CasualCodersProjects/Keyboard/Hardware/100p-keebored.kicad_sch

## KiCad design Hardware/100p-keebored.kicad_sch (2023-06-21)

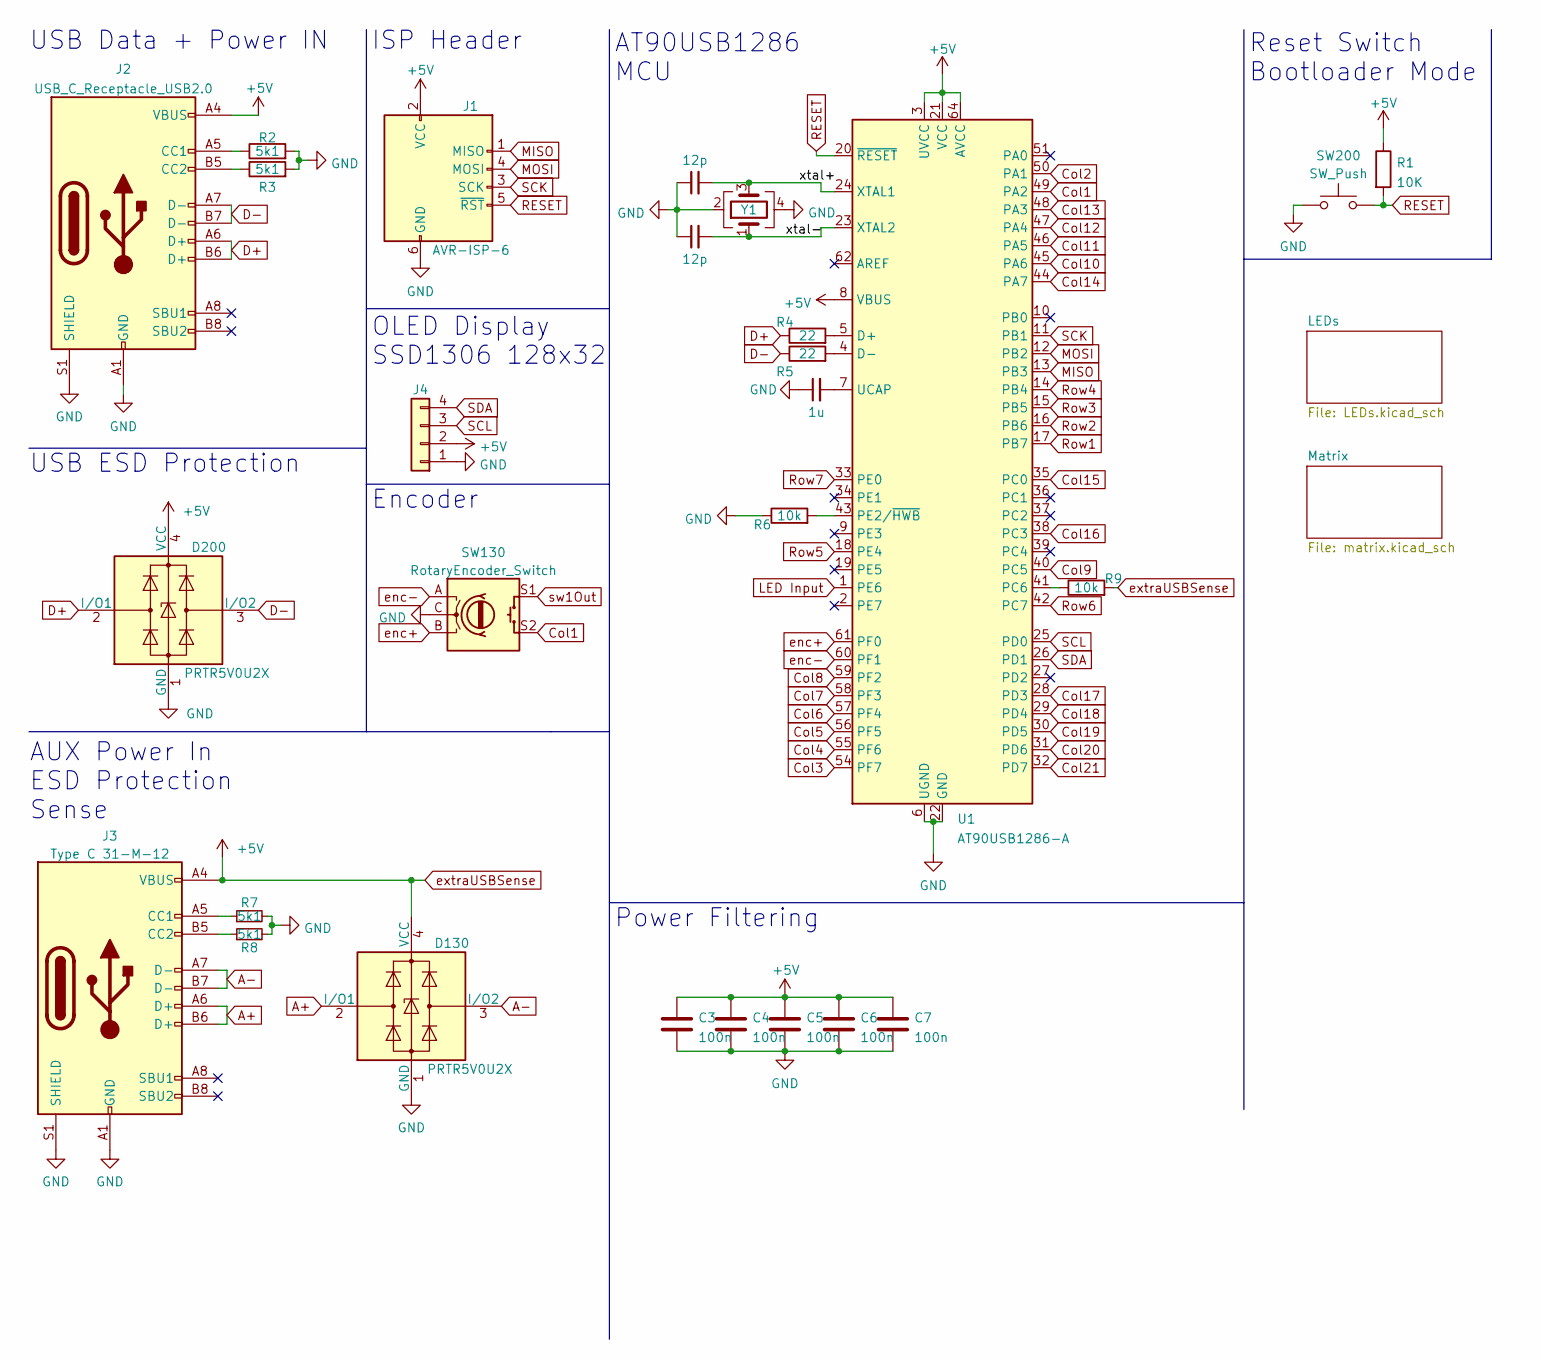
[picture p3: schematic 100p-keebored.kicad_sch]

Parts:
C1, C2: 12p; C_0402_1005Metric
C3, C4, C5, C6, C7: 100n; C_0402_1005Metric
C8: 1u; C_0402_1005Metric
D130, D200: PRTR5V0U2X; SOT-143
J1: AVR-ISP-6; Tag-Connect_TC2030-IDC-NL_2x03_P1.27mm_Vertical
J2: USB_C_Receptacle_USB2.0; USB_C_Receptacle_HRO_TYPE-C-31-M-12
J3: Type C 31-M-12; USB_C_Receptacle_HRO_TYPE-C-31-M-12
J4: Conn_01x04; SSD1306_128_32
R1: 10K; R_0402_1005Metric
R2, R3, R7, R8: 5k1; R_0402_1005Metric
R4, R5: 22; R_0402_1005Metric
R6, R9: 10k; R_0402_1005Metric
SW130: RotaryEncoder_Switch; RotaryEncoder_Alps_EC11E-Switch_Vertical_H20mm
SW200: SW_Push; SW_SPST_SKQG_WithStem
U1: AT90USB1286-A; TQFP-64_14x14mm_P0.8mm
Y1: JYJE 3TJ480000JYLBC; Crystal_SMD_3225-4Pin_3.2x2.5mm

Connections:
+5V: C3.1, C4.1, C5.1, C6.1, C7.1, D130.4 (VCC), D200.4 (VCC), J1.2 (VCC), J2.A4 (VBUS), J2.A9 (VBUS), J2.B4 (VBUS), J2.B9 (VBUS), J3.A4 (VBUS), J3.A9 (VBUS), J3.B4 (VBUS), J3.B9 (VBUS), J4.2, R1.1, R9.2, U1.3 (UVCC), U1.8 (VBUS), U1.21 (VCC), U1.52 (VCC), U1.64 (AVCC)
A+: D130.2 (I/O1), J3.A6 (D+), J3.B6 (D+)
A-: D130.3 (I/O2), J3.A7 (D-), J3.B7 (D-)
Col1: SW130.S2, U1.49 (PA2)
Col2: U1.50 (PA1)
Col3: U1.54 (PF7)
Col4: U1.55 (PF6)
Col5: U1.56 (PF5)
Col6: U1.57 (PF4)
Col7: U1.58 (PF3)
Col8: U1.59 (PF2)
Col9: U1.40 (PC5)
Col10: U1.45 (PA6)
Col11: U1.46 (PA5)
Col12: U1.47 (PA4)
Col13: U1.48 (PA3)
Col14: U1.44 (PA7)
Col15: U1.35 (PC0)
Col16: U1.38 (PC3)
Col17: U1.28 (PD3)
Col18: U1.29 (PD4)
Col19: U1.30 (PD5)
Col20: U1.31 (PD6)
Col21: U1.32 (PD7)
D+: D200.2 (I/O1), J2.A6 (D+), J2.B6 (D+), R4.1
D-: D200.3 (I/O2), J2.A7 (D-), J2.B7 (D-), R5.1
GND: C1.1, C2.1, C3.2, C4.2, C5.2, C6.2, C7.2, C8.1, D130.1 (GND), D200.1 (GND), J1.6 (GND), J2.A1 (GND), J2.A12 (GND), J2.B1 (GND), J2.B12 (GND), J2.S1 (SHIELD), J3.A1 (GND), J3.A12 (GND), J3.B1 (GND), J3.B12 (GND), J3.S1 (SHIELD), J4.1, R2.2, R3.2, R6.1, R7.2, R8.2, SW130.C, SW200.1, U1.6 (UGND), U1.22 (GND), U1.53 (GND), U1.63 (GND), Y1.2, Y1.4
LED Input: U1.1 (PE6)
MISO: J1.1 (MISO), U1.13 (PB3)
MOSI: J1.4 (MOSI), U1.12 (PB2)
unnamed: C8.2, U1.7 (UCAP)
unnamed: J2.A5 (CC1), R2.1
unnamed: J2.B5 (CC2), R3.1
unnamed: J3.A5 (CC1), R7.1
unnamed: J3.B5 (CC2), R8.1
unnamed: R4.2, U1.5 (D+)
unnamed: R5.2, U1.4 (D-)
unnamed: R6.2, U1.43 (PE2/~HWB)
unnamed: R9.1, U1.41 (PC6)
RESET: J1.5 (~RST), R1.2, SW200.2, U1.20 (~RESET)
Row1: U1.17 (PB7)
Row2: U1.16 (PB6)
Row3: U1.15 (PB5)
Row4: U1.14 (PB4)
Row5: U1.18 (PE4)
Row6: U1.42 (PC7)
Row7: U1.33 (PE0)
SCK: J1.3 (SCK), U1.11 (PB1)
SCL: J4.3, U1.25 (PD0)
SDA: J4.4, U1.26 (PD1)
enc+: SW130.B, U1.61 (PF0)
enc-: SW130.A, U1.60 (PF1)
sw1Out: SW130.S1
xtal+: C2.2, U1.24 (XTAL1), Y1.3
xtal-: C1.2, U1.23 (XTAL2), Y1.1

Notes on the sheet:
USB Data + Power IN
Encoder
OLED Display SSD1306 128x32
Power Filtering
AT90USB1286 MCU
AUX Power In ESD Protection Sense
ISP Header
USB ESD Protection
Reset Switch Bootloader Mode
