CasualCodersProjects/Keyboard/Hardware/LEDs.kicad_sch

## KiCad design Hardware/LEDs.kicad_sch (2023-06-21)

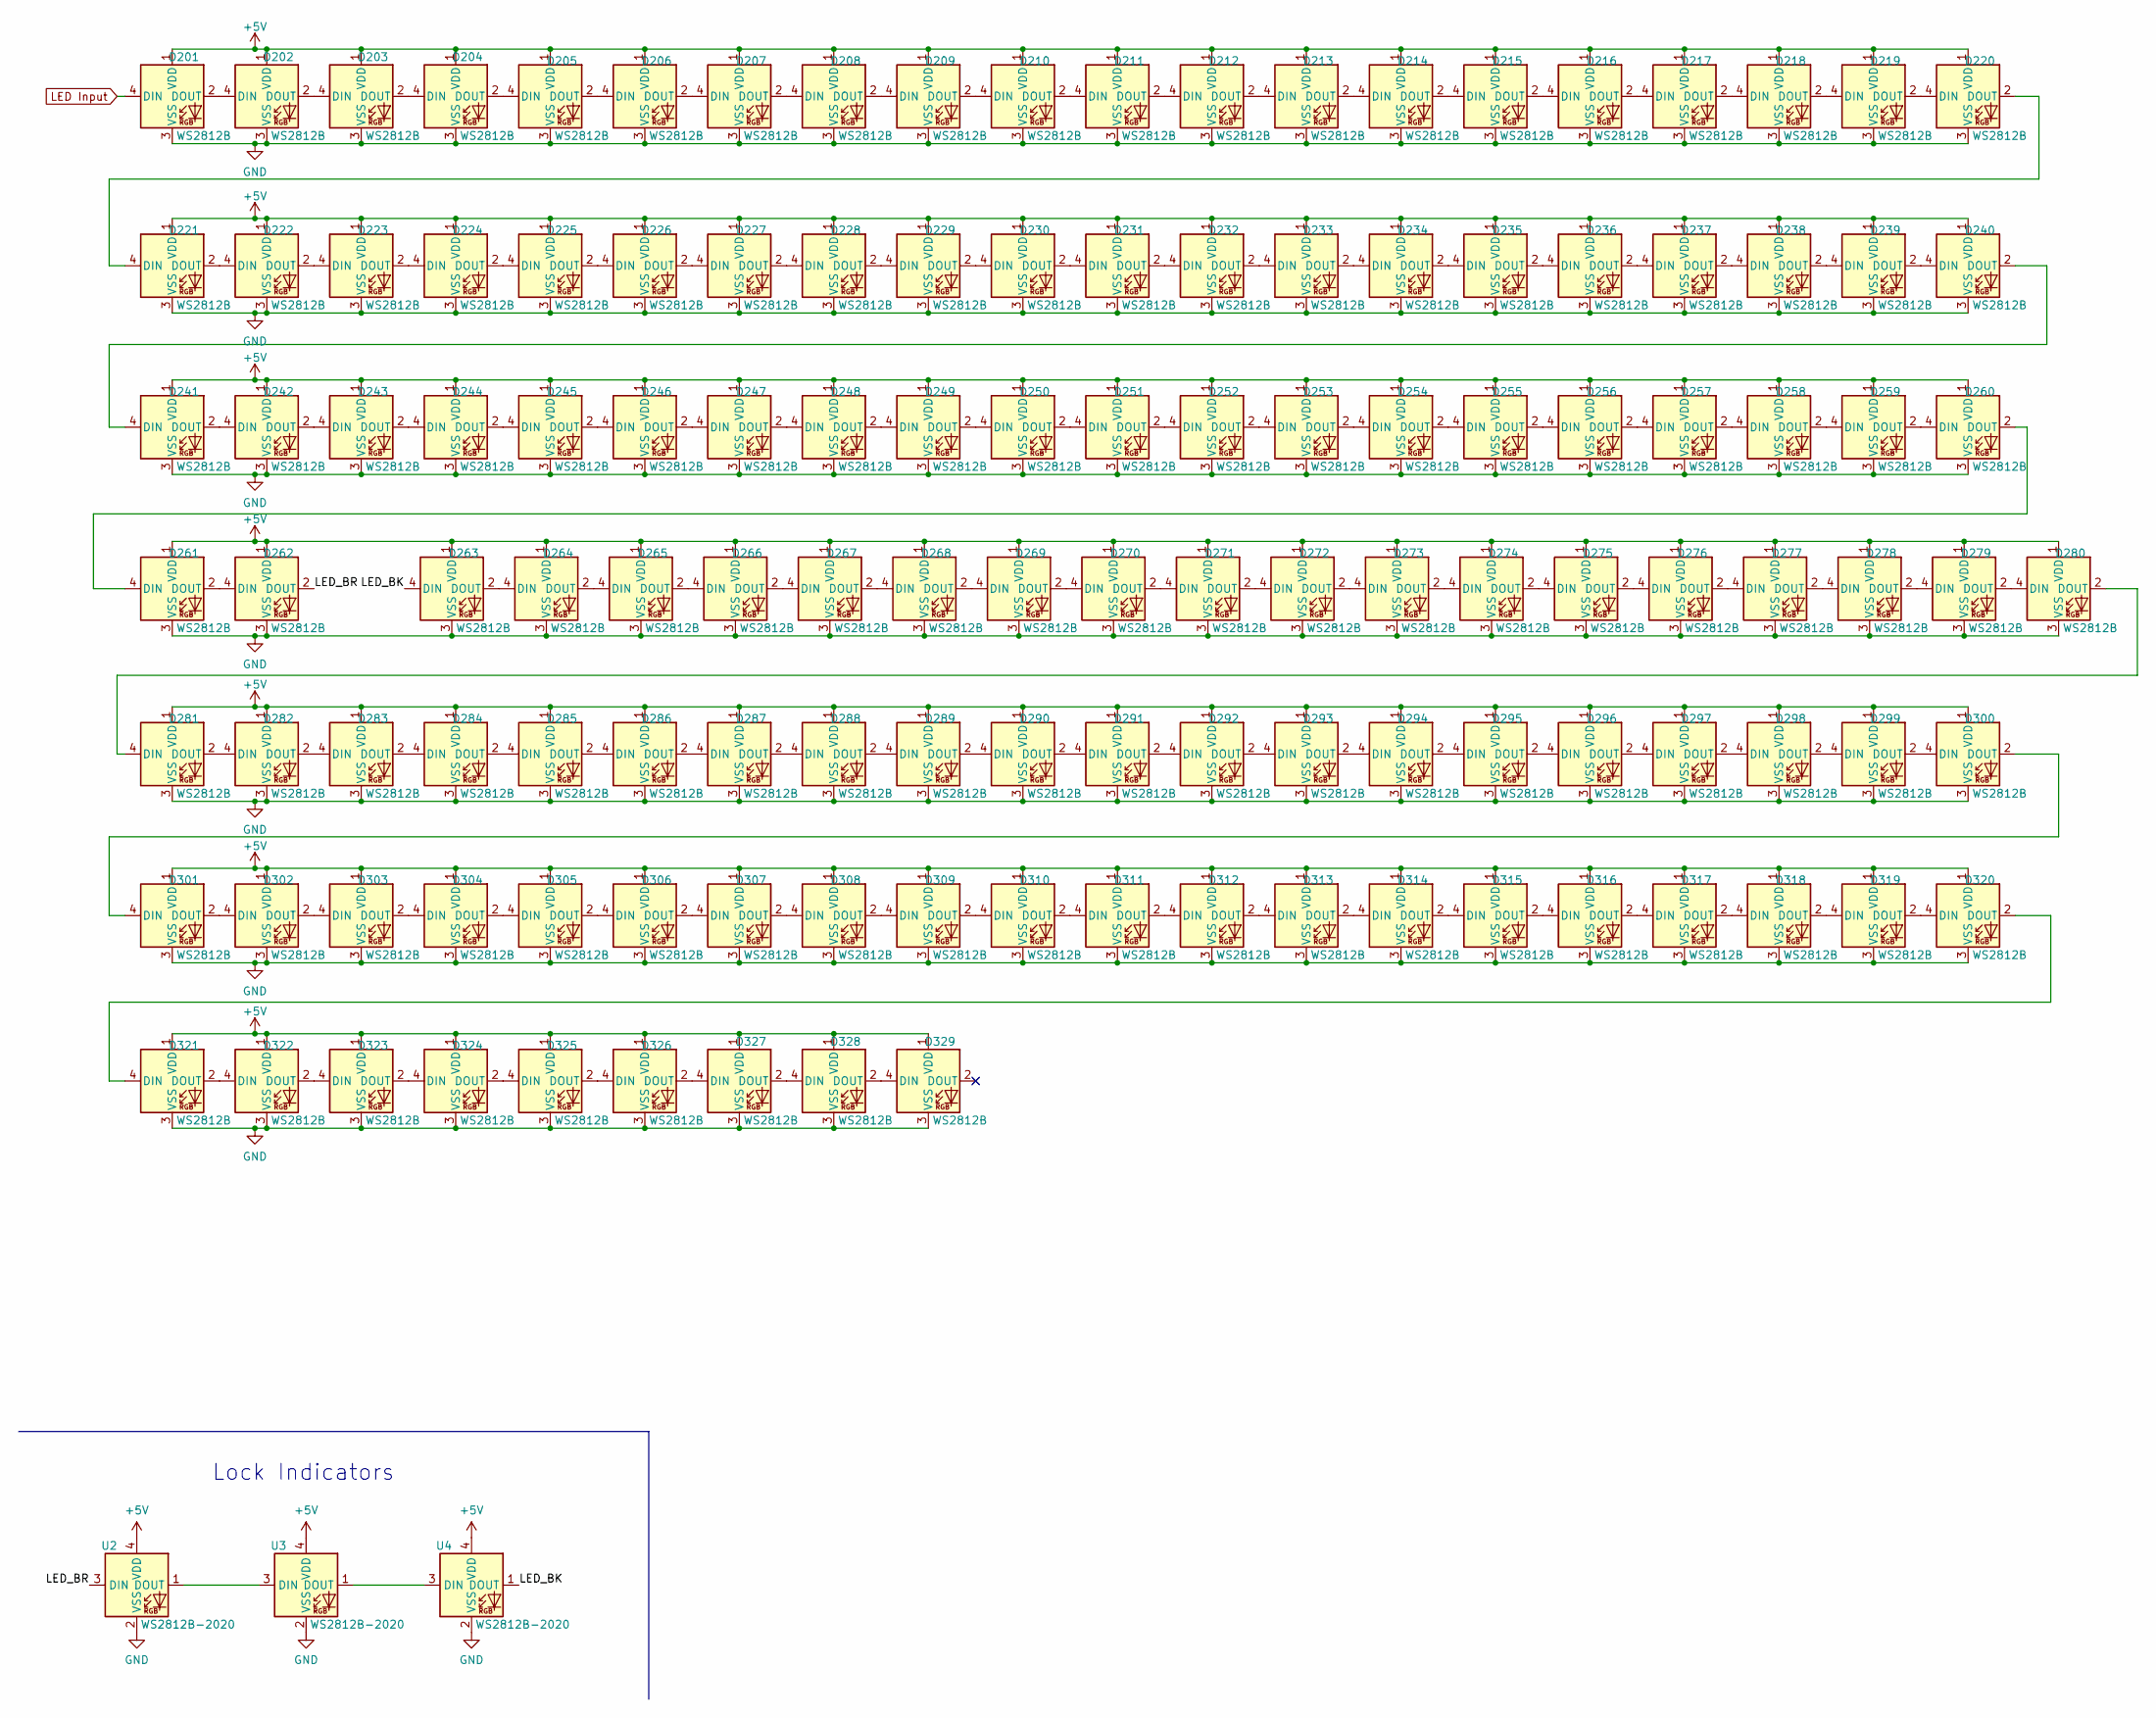
[picture p4: schematic LEDs.kicad_sch]

Parts:
D201, D202, D203, D204, D205, D206, D207, D208, D209, D210, D211, D212, D213, D214, D215, D216, D217, D218, D219, D220, D221, D222, D223, D224, D225, D226, D227, D228, D229, D230, D231, D232, D233, D234, D235, D236, D237, D238, D239, D240, D241, D242, D243, D244, D245, D246, D247, D248, D249, D250, D251, D252, D253, D254, D255, D256, D257, D258, D259, D260, D261, D262, D263, D264, D265, D266, D267, D268, D269, D270, D271, D272, D273, D274, D275, D276, D277, D278, D279, D280, D281, D282, D283, D284, D285, D286, D287, D288, D289, D290, D291, D292, D293, D294, D295, D296, D297, D298, D299, D300, D301, D302, D303, D304, D305, D306, D307, D308, D309, D310, D311, D312, D313, D314, D315, D316, D317, D318, D319, D320, D321, D322, D323, D324, D325, D326, D327, D328, D329: WS2812B; WS2812B-2020 ShineThrough
U2, U3, U4: WS2812B-2020; LED_WS2812B-2020_PLCC4_2.0x2.0mm

Connections:
+5V: D201.1 (VDD), D202.1 (VDD), D203.1 (VDD), D204.1 (VDD), D205.1 (VDD), D206.1 (VDD), D207.1 (VDD), D208.1 (VDD), D209.1 (VDD), D210.1 (VDD), D211.1 (VDD), D212.1 (VDD), D213.1 (VDD), D214.1 (VDD), D215.1 (VDD), D216.1 (VDD), D217.1 (VDD), D218.1 (VDD), D219.1 (VDD), D220.1 (VDD), D221.1 (VDD), D222.1 (VDD), D223.1 (VDD), D224.1 (VDD), D225.1 (VDD), D226.1 (VDD), D227.1 (VDD), D228.1 (VDD), D229.1 (VDD), D230.1 (VDD), D231.1 (VDD), D232.1 (VDD), D233.1 (VDD), D234.1 (VDD), D235.1 (VDD), D236.1 (VDD), D237.1 (VDD), D238.1 (VDD), D239.1 (VDD), D240.1 (VDD), D241.1 (VDD), D242.1 (VDD), D243.1 (VDD), D244.1 (VDD), D245.1 (VDD), D246.1 (VDD), D247.1 (VDD), D248.1 (VDD), D249.1 (VDD), D250.1 (VDD), D251.1 (VDD), D252.1 (VDD), D253.1 (VDD), D254.1 (VDD), D255.1 (VDD), D256.1 (VDD), D257.1 (VDD), D258.1 (VDD), D259.1 (VDD), D260.1 (VDD), D261.1 (VDD), D262.1 (VDD), D263.1 (VDD), D264.1 (VDD), D265.1 (VDD), D266.1 (VDD), D267.1 (VDD), D268.1 (VDD), D269.1 (VDD), D270.1 (VDD), D271.1 (VDD), D272.1 (VDD), D273.1 (VDD), D274.1 (VDD), D275.1 (VDD), D276.1 (VDD), D277.1 (VDD), D278.1 (VDD), D279.1 (VDD), D280.1 (VDD), D281.1 (VDD), D282.1 (VDD), D283.1 (VDD), D284.1 (VDD), D285.1 (VDD), D286.1 (VDD), D287.1 (VDD), D288.1 (VDD), D289.1 (VDD), D290.1 (VDD), D291.1 (VDD), D292.1 (VDD), D293.1 (VDD), D294.1 (VDD), D295.1 (VDD), D296.1 (VDD), D297.1 (VDD), D298.1 (VDD), D299.1 (VDD), D300.1 (VDD), D301.1 (VDD), D302.1 (VDD), D303.1 (VDD), D304.1 (VDD), D305.1 (VDD), D306.1 (VDD), D307.1 (VDD), D308.1 (VDD), D309.1 (VDD), D310.1 (VDD), D311.1 (VDD), D312.1 (VDD), D313.1 (VDD), D314.1 (VDD), D315.1 (VDD), D316.1 (VDD), D317.1 (VDD), D318.1 (VDD), D319.1 (VDD), D320.1 (VDD), D321.1 (VDD), D322.1 (VDD), D323.1 (VDD), D324.1 (VDD), D325.1 (VDD), D326.1 (VDD), D327.1 (VDD), D328.1 (VDD), D329.1 (VDD), U2.4 (VDD), U3.4 (VDD), U4.4 (VDD)
GND: D201.3 (VSS), D202.3 (VSS), D203.3 (VSS), D204.3 (VSS), D205.3 (VSS), D206.3 (VSS), D207.3 (VSS), D208.3 (VSS), D209.3 (VSS), D210.3 (VSS), D211.3 (VSS), D212.3 (VSS), D213.3 (VSS), D214.3 (VSS), D215.3 (VSS), D216.3 (VSS), D217.3 (VSS), D218.3 (VSS), D219.3 (VSS), D220.3 (VSS), D221.3 (VSS), D222.3 (VSS), D223.3 (VSS), D224.3 (VSS), D225.3 (VSS), D226.3 (VSS), D227.3 (VSS), D228.3 (VSS), D229.3 (VSS), D230.3 (VSS), D231.3 (VSS), D232.3 (VSS), D233.3 (VSS), D234.3 (VSS), D235.3 (VSS), D236.3 (VSS), D237.3 (VSS), D238.3 (VSS), D239.3 (VSS), D240.3 (VSS), D241.3 (VSS), D242.3 (VSS), D243.3 (VSS), D244.3 (VSS), D245.3 (VSS), D246.3 (VSS), D247.3 (VSS), D248.3 (VSS), D249.3 (VSS), D250.3 (VSS), D251.3 (VSS), D252.3 (VSS), D253.3 (VSS), D254.3 (VSS), D255.3 (VSS), D256.3 (VSS), D257.3 (VSS), D258.3 (VSS), D259.3 (VSS), D260.3 (VSS), D261.3 (VSS), D262.3 (VSS), D263.3 (VSS), D264.3 (VSS), D265.3 (VSS), D266.3 (VSS), D267.3 (VSS), D268.3 (VSS), D269.3 (VSS), D270.3 (VSS), D271.3 (VSS), D272.3 (VSS), D273.3 (VSS), D274.3 (VSS), D275.3 (VSS), D276.3 (VSS), D277.3 (VSS), D278.3 (VSS), D279.3 (VSS), D280.3 (VSS), D281.3 (VSS), D282.3 (VSS), D283.3 (VSS), D284.3 (VSS), D285.3 (VSS), D286.3 (VSS), D287.3 (VSS), D288.3 (VSS), D289.3 (VSS), D290.3 (VSS), D291.3 (VSS), D292.3 (VSS), D293.3 (VSS), D294.3 (VSS), D295.3 (VSS), D296.3 (VSS), D297.3 (VSS), D298.3 (VSS), D299.3 (VSS), D300.3 (VSS), D301.3 (VSS), D302.3 (VSS), D303.3 (VSS), D304.3 (VSS), D305.3 (VSS), D306.3 (VSS), D307.3 (VSS), D308.3 (VSS), D309.3 (VSS), D310.3 (VSS), D311.3 (VSS), D312.3 (VSS), D313.3 (VSS), D314.3 (VSS), D315.3 (VSS), D316.3 (VSS), D317.3 (VSS), D318.3 (VSS), D319.3 (VSS), D320.3 (VSS), D321.3 (VSS), D322.3 (VSS), D323.3 (VSS), D324.3 (VSS), D325.3 (VSS), D326.3 (VSS), D327.3 (VSS), D328.3 (VSS), D329.3 (VSS), U2.2 (VSS), U3.2 (VSS), U4.2 (VSS)
LED Input: D201.4 (DIN)
LED_BK: D263.4 (DIN), U4.1 (DOUT)
LED_BR: D262.2 (DOUT), U2.3 (DIN)
unnamed: D201.2 (DOUT), D202.4 (DIN)
unnamed: D202.2 (DOUT), D203.4 (DIN)
unnamed: D203.2 (DOUT), D204.4 (DIN)
unnamed: D204.2 (DOUT), D205.4 (DIN)
unnamed: D205.2 (DOUT), D206.4 (DIN)
unnamed: D206.2 (DOUT), D207.4 (DIN)
unnamed: D207.2 (DOUT), D208.4 (DIN)
unnamed: D208.2 (DOUT), D209.4 (DIN)
unnamed: D209.2 (DOUT), D210.4 (DIN)
unnamed: D210.2 (DOUT), D211.4 (DIN)
unnamed: D211.2 (DOUT), D212.4 (DIN)
unnamed: D212.2 (DOUT), D213.4 (DIN)
unnamed: D213.2 (DOUT), D214.4 (DIN)
unnamed: D214.2 (DOUT), D215.4 (DIN)
unnamed: D215.2 (DOUT), D216.4 (DIN)
unnamed: D216.2 (DOUT), D217.4 (DIN)
unnamed: D217.2 (DOUT), D218.4 (DIN)
unnamed: D218.2 (DOUT), D219.4 (DIN)
unnamed: D219.2 (DOUT), D220.4 (DIN)
unnamed: D220.2 (DOUT), D221.4 (DIN)
unnamed: D221.2 (DOUT), D222.4 (DIN)
unnamed: D222.2 (DOUT), D223.4 (DIN)
unnamed: D223.2 (DOUT), D224.4 (DIN)
unnamed: D224.2 (DOUT), D225.4 (DIN)
unnamed: D225.2 (DOUT), D226.4 (DIN)
unnamed: D226.2 (DOUT), D227.4 (DIN)
unnamed: D227.2 (DOUT), D228.4 (DIN)
unnamed: D228.2 (DOUT), D229.4 (DIN)
unnamed: D229.2 (DOUT), D230.4 (DIN)
unnamed: D230.2 (DOUT), D231.4 (DIN)
unnamed: D231.2 (DOUT), D232.4 (DIN)
unnamed: D232.2 (DOUT), D233.4 (DIN)
unnamed: D233.2 (DOUT), D234.4 (DIN)
unnamed: D234.2 (DOUT), D235.4 (DIN)
unnamed: D235.2 (DOUT), D236.4 (DIN)
unnamed: D236.2 (DOUT), D237.4 (DIN)
unnamed: D237.2 (DOUT), D238.4 (DIN)
unnamed: D238.2 (DOUT), D239.4 (DIN)
unnamed: D239.2 (DOUT), D240.4 (DIN)
unnamed: D240.2 (DOUT), D241.4 (DIN)
unnamed: D241.2 (DOUT), D242.4 (DIN)
unnamed: D242.2 (DOUT), D243.4 (DIN)
unnamed: D243.2 (DOUT), D244.4 (DIN)
unnamed: D244.2 (DOUT), D245.4 (DIN)
unnamed: D245.2 (DOUT), D246.4 (DIN)
unnamed: D246.2 (DOUT), D247.4 (DIN)
unnamed: D247.2 (DOUT), D248.4 (DIN)
unnamed: D248.2 (DOUT), D249.4 (DIN)
unnamed: D249.2 (DOUT), D250.4 (DIN)
unnamed: D250.2 (DOUT), D251.4 (DIN)
unnamed: D251.2 (DOUT), D252.4 (DIN)
unnamed: D252.2 (DOUT), D253.4 (DIN)
unnamed: D253.2 (DOUT), D254.4 (DIN)
unnamed: D254.2 (DOUT), D255.4 (DIN)
unnamed: D255.2 (DOUT), D256.4 (DIN)
unnamed: D256.2 (DOUT), D257.4 (DIN)
unnamed: D257.2 (DOUT), D258.4 (DIN)
unnamed: D258.2 (DOUT), D259.4 (DIN)
unnamed: D259.2 (DOUT), D260.4 (DIN)
unnamed: D260.2 (DOUT), D261.4 (DIN)
unnamed: D261.2 (DOUT), D262.4 (DIN)
unnamed: D263.2 (DOUT), D264.4 (DIN)
unnamed: D264.2 (DOUT), D265.4 (DIN)
unnamed: D265.2 (DOUT), D266.4 (DIN)
unnamed: D266.2 (DOUT), D267.4 (DIN)
unnamed: D267.2 (DOUT), D268.4 (DIN)
unnamed: D268.2 (DOUT), D269.4 (DIN)
unnamed: D269.2 (DOUT), D270.4 (DIN)
unnamed: D270.2 (DOUT), D271.4 (DIN)
unnamed: D271.2 (DOUT), D272.4 (DIN)
unnamed: D272.2 (DOUT), D273.4 (DIN)
unnamed: D273.2 (DOUT), D274.4 (DIN)
unnamed: D274.2 (DOUT), D275.4 (DIN)
unnamed: D275.2 (DOUT), D276.4 (DIN)
unnamed: D276.2 (DOUT), D277.4 (DIN)
unnamed: D277.2 (DOUT), D278.4 (DIN)
unnamed: D278.2 (DOUT), D279.4 (DIN)
unnamed: D279.2 (DOUT), D280.4 (DIN)
unnamed: D280.2 (DOUT), D281.4 (DIN)
unnamed: D281.2 (DOUT), D282.4 (DIN)
unnamed: D282.2 (DOUT), D283.4 (DIN)
unnamed: D283.2 (DOUT), D284.4 (DIN)
unnamed: D284.2 (DOUT), D285.4 (DIN)
unnamed: D285.2 (DOUT), D286.4 (DIN)
unnamed: D286.2 (DOUT), D287.4 (DIN)
unnamed: D287.2 (DOUT), D288.4 (DIN)
unnamed: D288.2 (DOUT), D289.4 (DIN)
unnamed: D289.2 (DOUT), D290.4 (DIN)
unnamed: D290.2 (DOUT), D291.4 (DIN)
unnamed: D291.2 (DOUT), D292.4 (DIN)
unnamed: D292.2 (DOUT), D293.4 (DIN)
unnamed: D293.2 (DOUT), D294.4 (DIN)
unnamed: D294.2 (DOUT), D295.4 (DIN)
unnamed: D295.2 (DOUT), D296.4 (DIN)
unnamed: D296.2 (DOUT), D297.4 (DIN)
unnamed: D297.2 (DOUT), D298.4 (DIN)
unnamed: D298.2 (DOUT), D299.4 (DIN)
unnamed: D299.2 (DOUT), D300.4 (DIN)
unnamed: D300.2 (DOUT), D301.4 (DIN)
unnamed: D301.2 (DOUT), D302.4 (DIN)
unnamed: D302.2 (DOUT), D303.4 (DIN)
unnamed: D303.2 (DOUT), D304.4 (DIN)
unnamed: D304.2 (DOUT), D305.4 (DIN)
unnamed: D305.2 (DOUT), D306.4 (DIN)
unnamed: D306.2 (DOUT), D307.4 (DIN)
unnamed: D307.2 (DOUT), D308.4 (DIN)
unnamed: D308.2 (DOUT), D309.4 (DIN)
unnamed: D309.2 (DOUT), D310.4 (DIN)
unnamed: D310.2 (DOUT), D311.4 (DIN)
unnamed: D311.2 (DOUT), D312.4 (DIN)
unnamed: D312.2 (DOUT), D313.4 (DIN)
unnamed: D313.2 (DOUT), D314.4 (DIN)
unnamed: D314.2 (DOUT), D315.4 (DIN)
unnamed: D315.2 (DOUT), D316.4 (DIN)
unnamed: D316.2 (DOUT), D317.4 (DIN)
unnamed: D317.2 (DOUT), D318.4 (DIN)
unnamed: D318.2 (DOUT), D319.4 (DIN)
unnamed: D319.2 (DOUT), D320.4 (DIN)
unnamed: D320.2 (DOUT), D321.4 (DIN)
unnamed: D321.2 (DOUT), D322.4 (DIN)
unnamed: D322.2 (DOUT), D323.4 (DIN)
unnamed: D323.2 (DOUT), D324.4 (DIN)
unnamed: D324.2 (DOUT), D325.4 (DIN)
unnamed: D325.2 (DOUT), D326.4 (DIN)
unnamed: D326.2 (DOUT), D327.4 (DIN)
unnamed: D327.2 (DOUT), D328.4 (DIN)
unnamed: D328.2 (DOUT), D329.4 (DIN)
unnamed: U2.1 (DOUT), U3.3 (DIN)
unnamed: U3.1 (DOUT), U4.3 (DIN)

Notes on the sheet:
Lock Indicators
